iuliaandreea30/TSC_prj/Images/PCB 2D.png

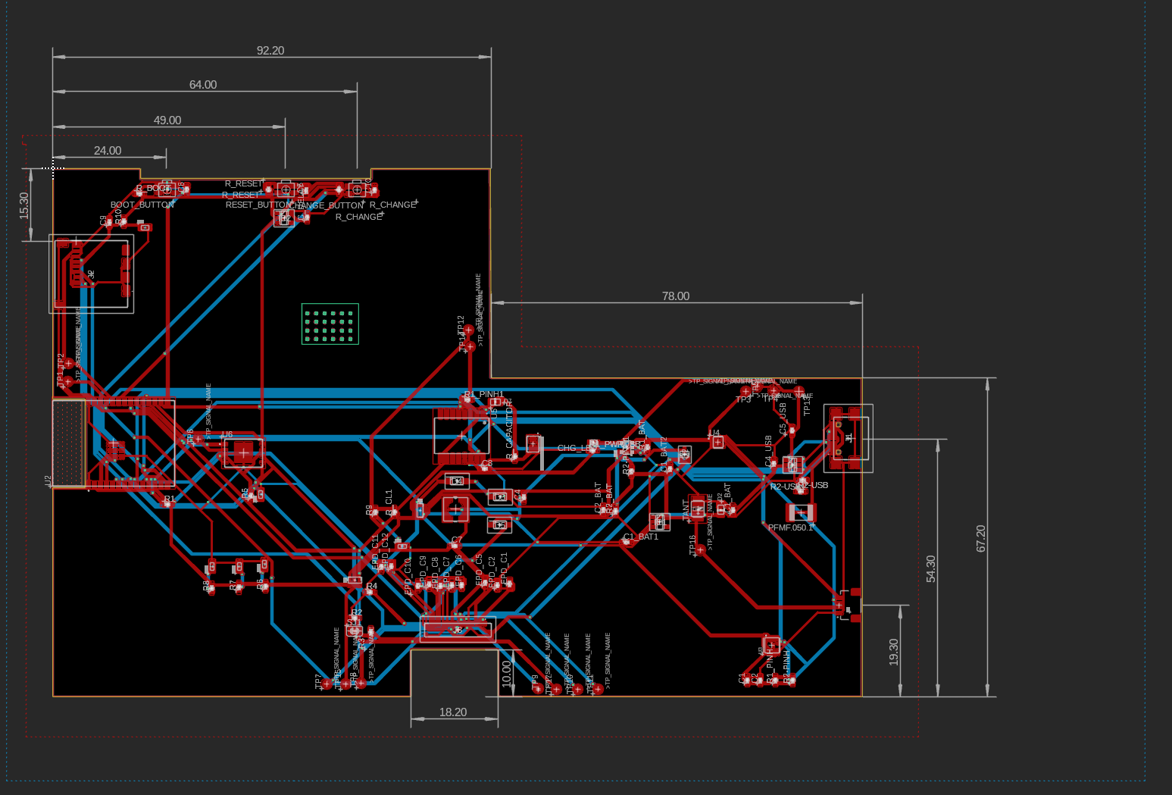
Images/PCB 2D.png
